Anton-Schoultz/HomeBrew/DataSheets/Switch_BinaryDial.png

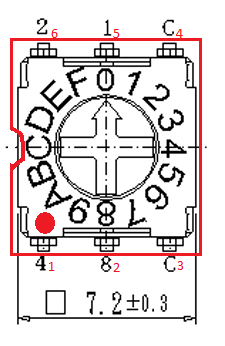
DataSheets/Switch_BinaryDial.png
