Anton-Schoultz/HomeBrew/Tools/LogicAnalyser/Pi-Pico-adapter-board.jpg

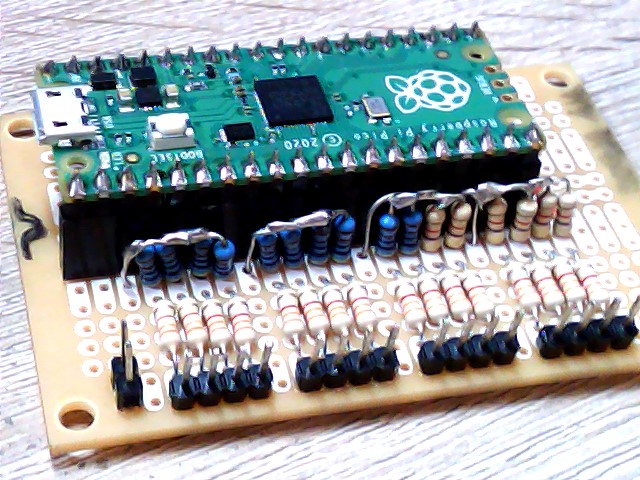
Tools/LogicAnalyser/Pi-Pico-adapter-board.jpg
